mhgolkar/Melon_Green/Documentation/0_Readme_MG_Image.jpg

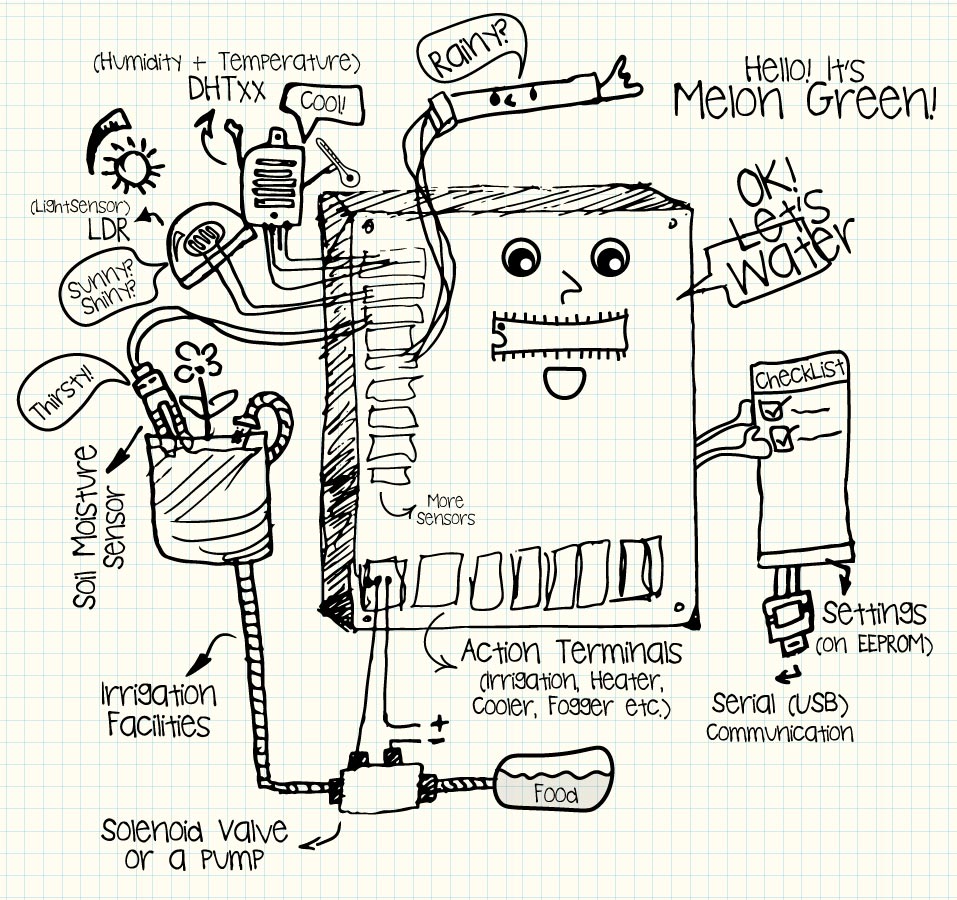
Documentation/0_Readme_MG_Image.jpg
