mhgolkar/Melon_Green/Documentation/1_Melon_Green_Board_[DIY]/MG_1.0.0_SFx_Layout.png

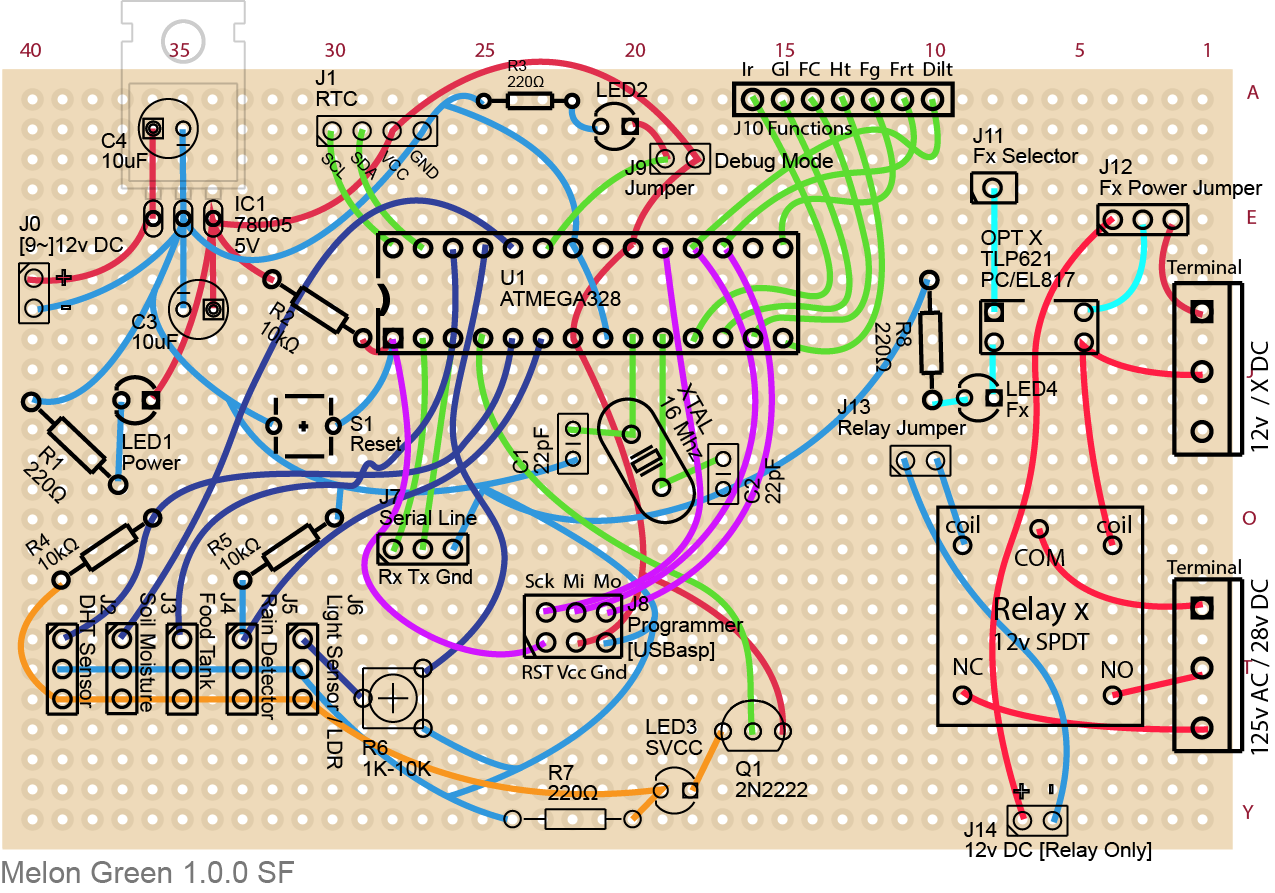
Documentation/1_Melon_Green_Board_[DIY]/MG_1.0.0_SFx_Layout.png
